Gloeidraad/SN74141-Substitution/Doc/DIL-Header.jpg

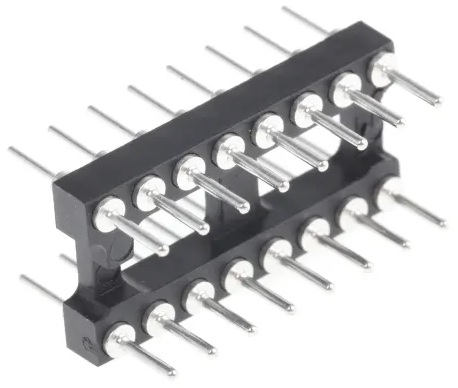
Doc/DIL-Header.jpg
