Gloeidraad/SN74141-Substitution/Doc/sch.png

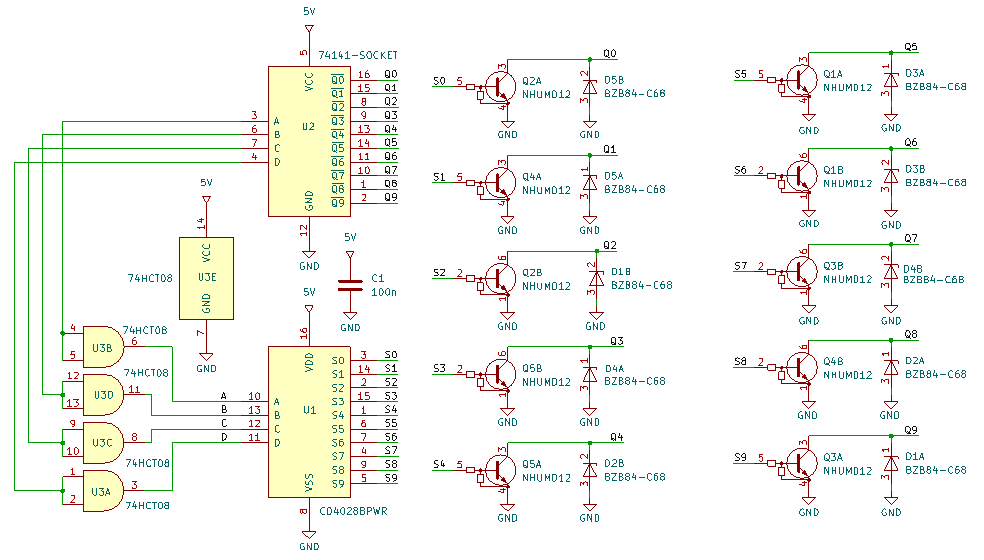
Doc/sch.png
